dan-rodrigues/ym2610-pcb/fw/mem_util.c

// mem_util.c
//
// Copyright (C) 2021 Dan Rodrigues <danrr.gh.oss@gmail.com>
//
// SPDX-License-Identifier: MIT

#include "mem_util.h"

uint32_t read32(const uint8_t *bytes) {
	uint32_t word = bytes[0];
	word |= bytes[1] << 8;
	word |= bytes[2] << 16;
	word |= bytes[3] << 24;

	return word;
}

// Using for / while loops here generated suboptimal code
// The do-while wrapped in an if statement looks odd but the inner loop is tighter

__attribute__ ((used))
__attribute__((optimize("-fno-strict-aliasing")))
void *memcpy(void *s1, const void *s2, size_t n) {
	// 32bit aligned part

	uint32_t *s1_32 = s1;
	const uint32_t *s2_32 = s2;

	if (!(((uintptr_t)s1 | (uintptr_t)s2) & 3) && n >= 4) {
		uint32_t copied_words = n / 4;
		const uint32_t * const s1_end = s1_32 + copied_words;

		 do {
			*s1_32++ = *s2_32++;
		 } while (s1_32 < s1_end);

		n -= copied_words * 4;
	}

	// Unaligned part

	char *c1 = (char *)s1_32;
	const char *c2 = (const char *)s2_32;

	const char * const c1_end = c1 + n;

	if (n > 0) {
		do {
			*c1++ = *c2++;
		} while (c1 < c1_end);
	}

	return s1;
}
